Fred72z/ALICE/Cartouche/Etiquettes/4K_FlagonBird_Etiquette.png

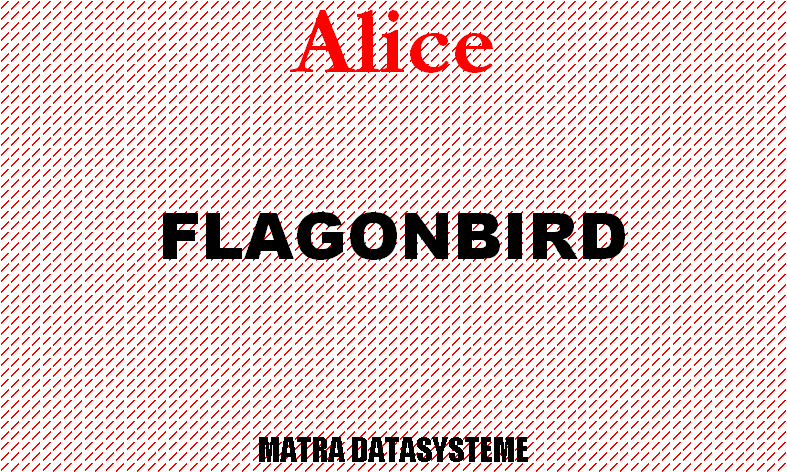
Cartouche/Etiquettes/4K_FlagonBird_Etiquette.png
