Fred72z/ALICE/Cartouche/Etiquettes/4K_LostWorld_Etiquette.png

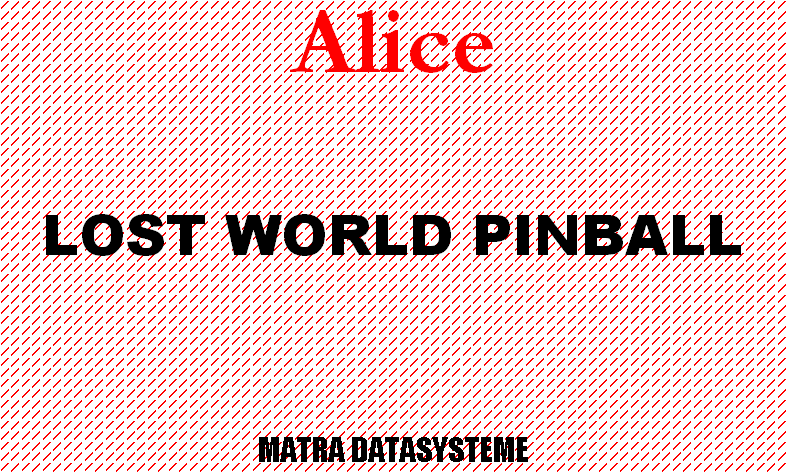
Cartouche/Etiquettes/4K_LostWorld_Etiquette.png
