Fred72z/ALICE/Cartouche/Etiquettes/Chenille_Etiquette.png

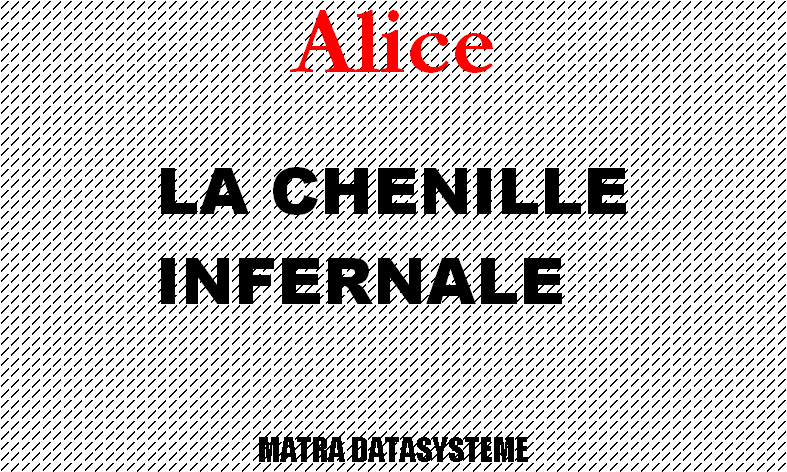
Cartouche/Etiquettes/Chenille_Etiquette.png
