Fred72z/ALICE/Cartouche/Etiquettes/Crocky_Etiquette.png

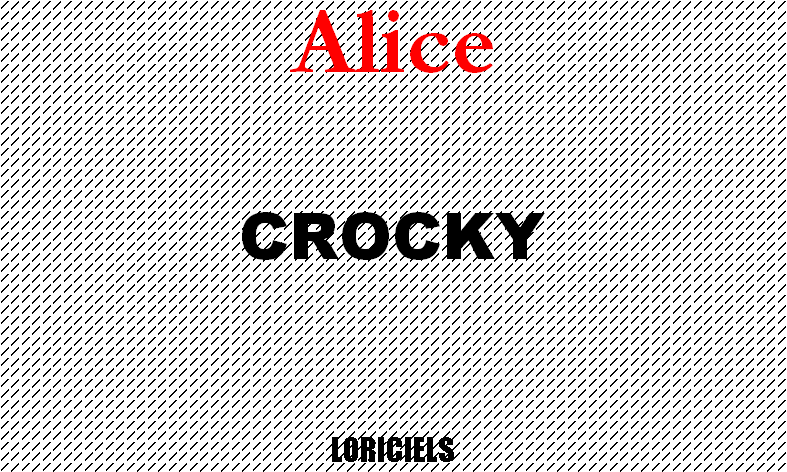
Cartouche/Etiquettes/Crocky_Etiquette.png
