Fred72z/ALICE/Cartouche/Etiquettes/Fringale_Etiquette.png

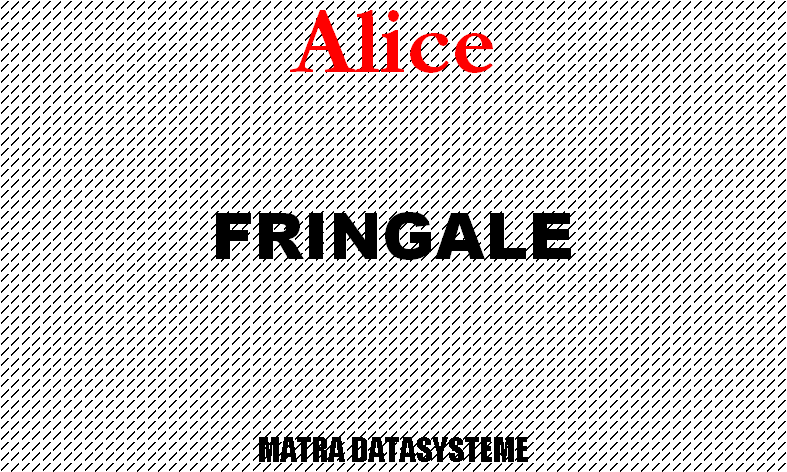
Cartouche/Etiquettes/Fringale_Etiquette.png
