Fred72z/ALICE/Cartouche/Etiquettes/PillageCosmique_Etiquette.png

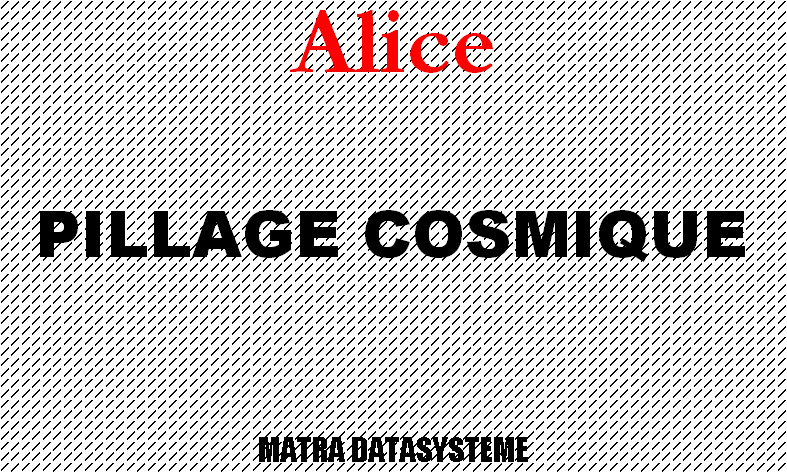
Cartouche/Etiquettes/PillageCosmique_Etiquette.png
