Fred72z/ALICE/Cartouche/Etiquettes/Tank_Etiquette.png

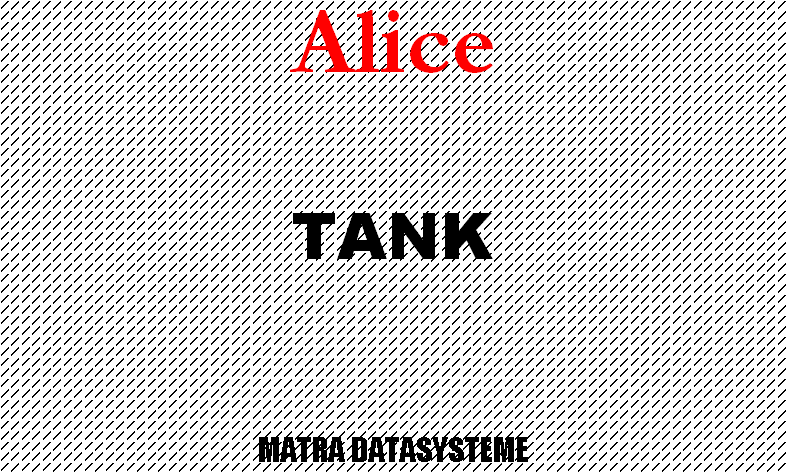
Cartouche/Etiquettes/Tank_Etiquette.png
