Fred72z/ALICE/Cartouche/Jaquettes/4K_FlagonBird_Jaquette.png

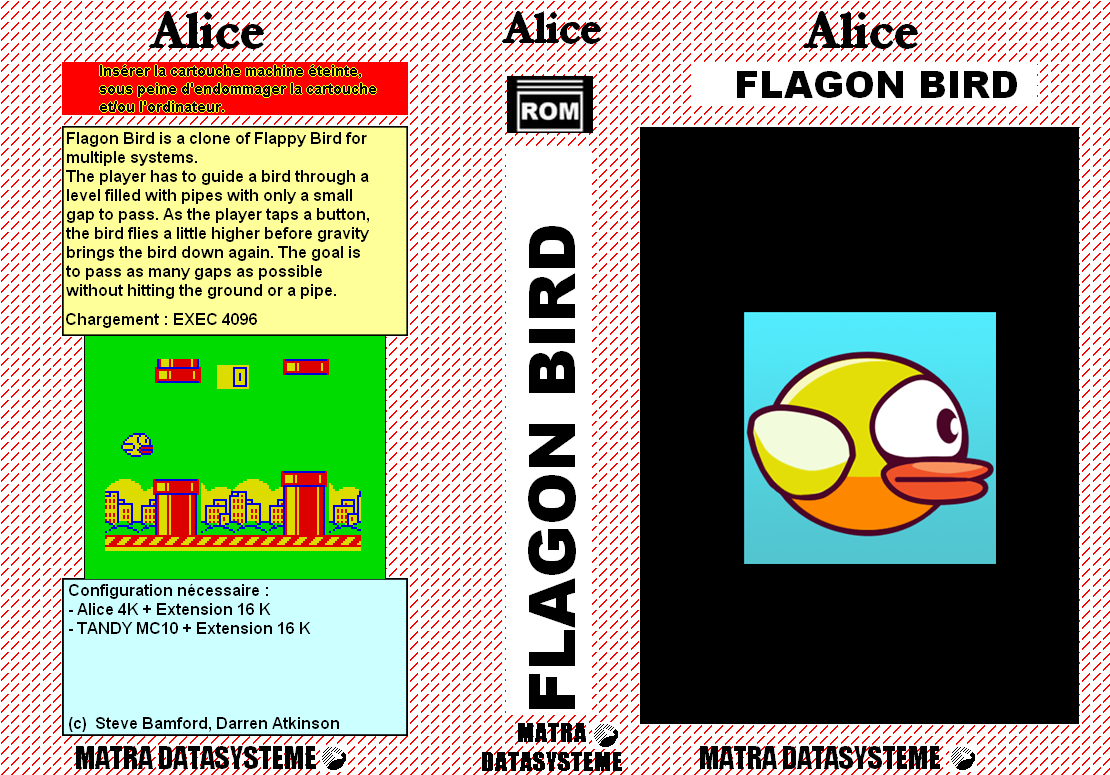
Cartouche/Jaquettes/4K_FlagonBird_Jaquette.png
