Fred72z/ALICE/Cartouche/Jaquettes/4K_Pacman_Jaquette.png

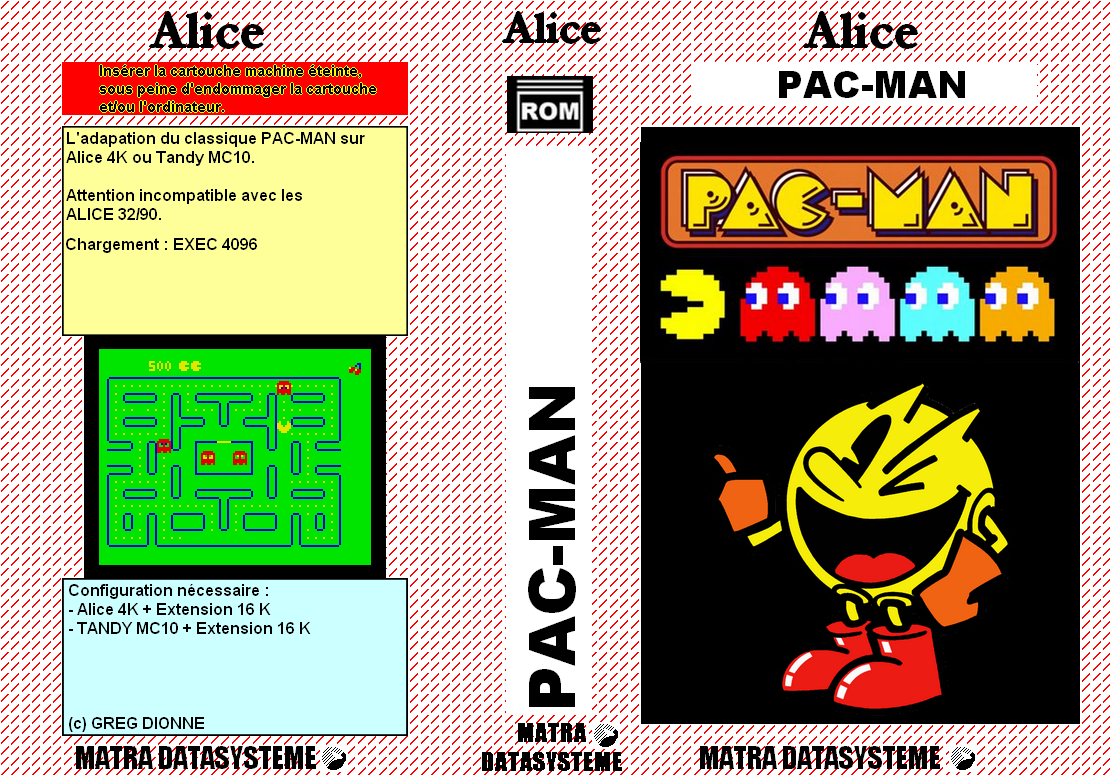
Cartouche/Jaquettes/4K_Pacman_Jaquette.png
