Fred72z/ALICE/Cartouche/Jaquettes/Chenille_Jaquette.png

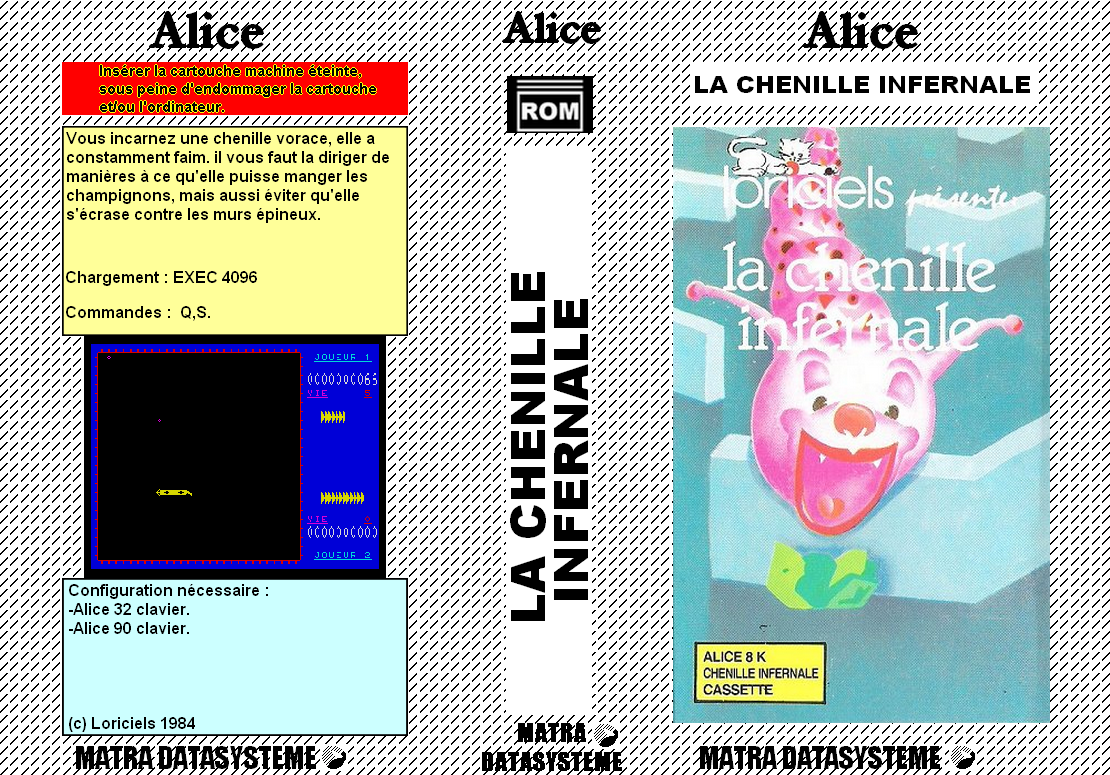
Cartouche/Jaquettes/Chenille_Jaquette.png
