Fred72z/ALICE/Cartouche/Jaquettes/Crocky_Jaquette.png

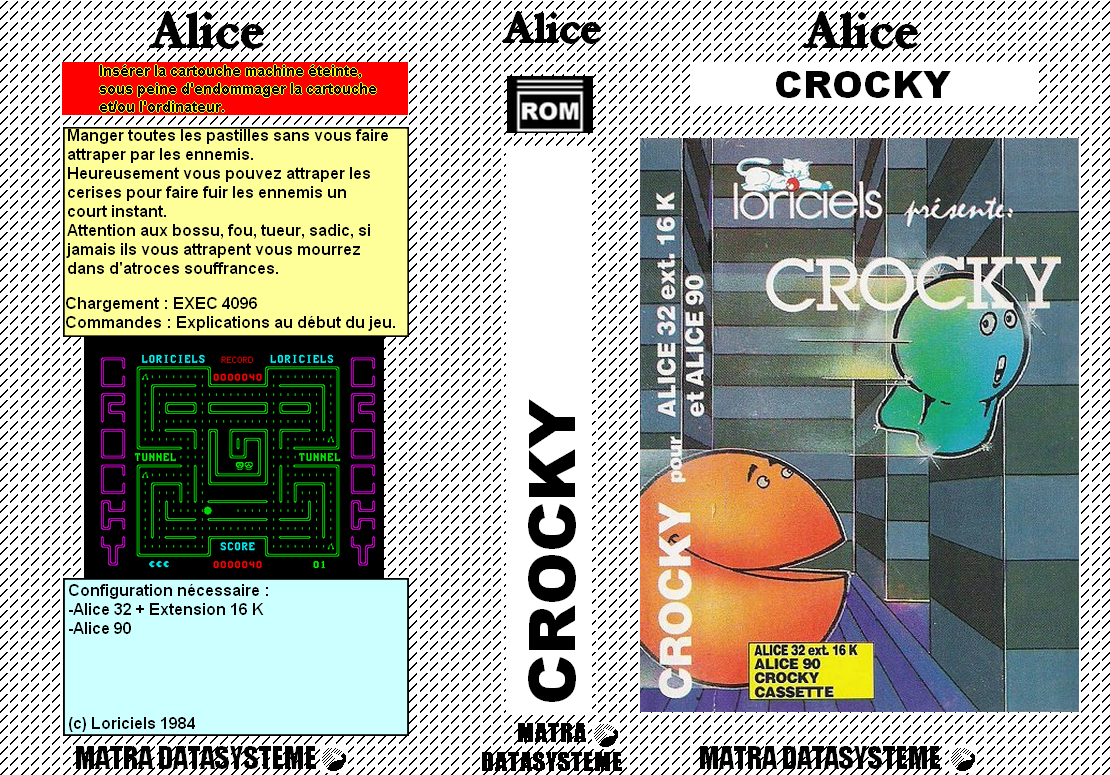
Cartouche/Jaquettes/Crocky_Jaquette.png
