Fred72z/ALICE/Cartouche/Jaquettes/DessineMoi_Jaquette.png

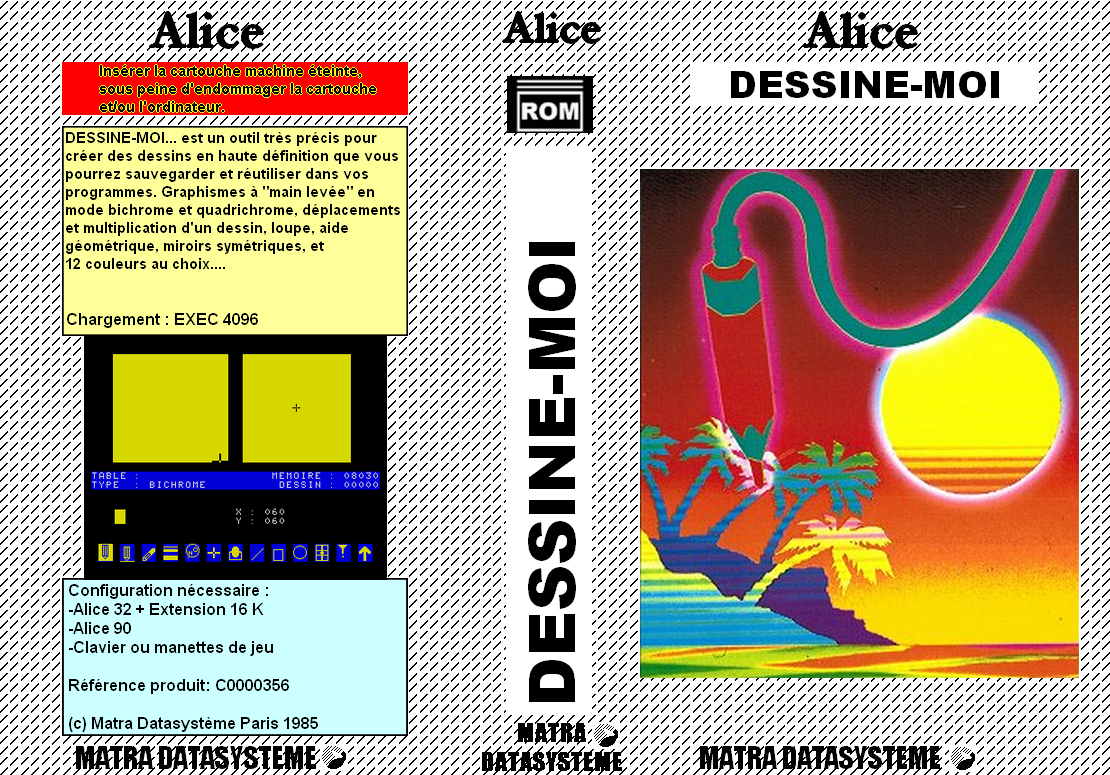
Cartouche/Jaquettes/DessineMoi_Jaquette.png
