Fred72z/ALICE/Cartouche/Jaquettes/Fringale90_Jaquette.png

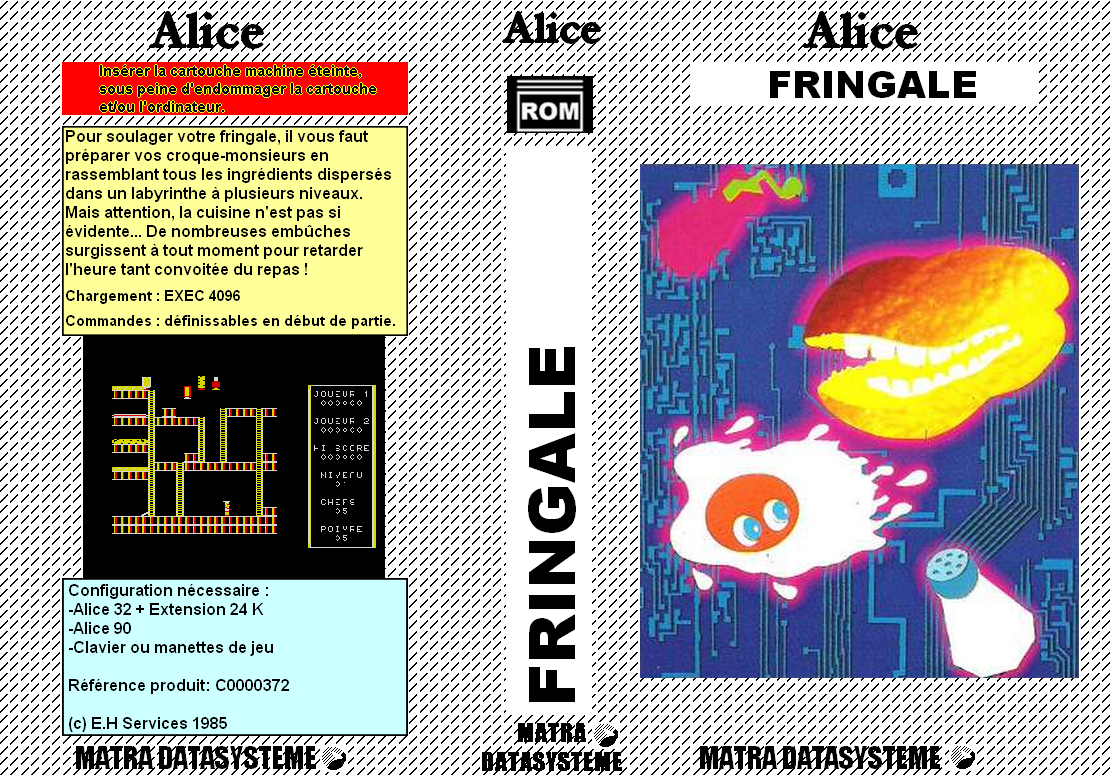
Cartouche/Jaquettes/Fringale90_Jaquette.png
