Fred72z/ALICE/Cartouche/Jaquettes/PillageCosmique_Jaquette.png

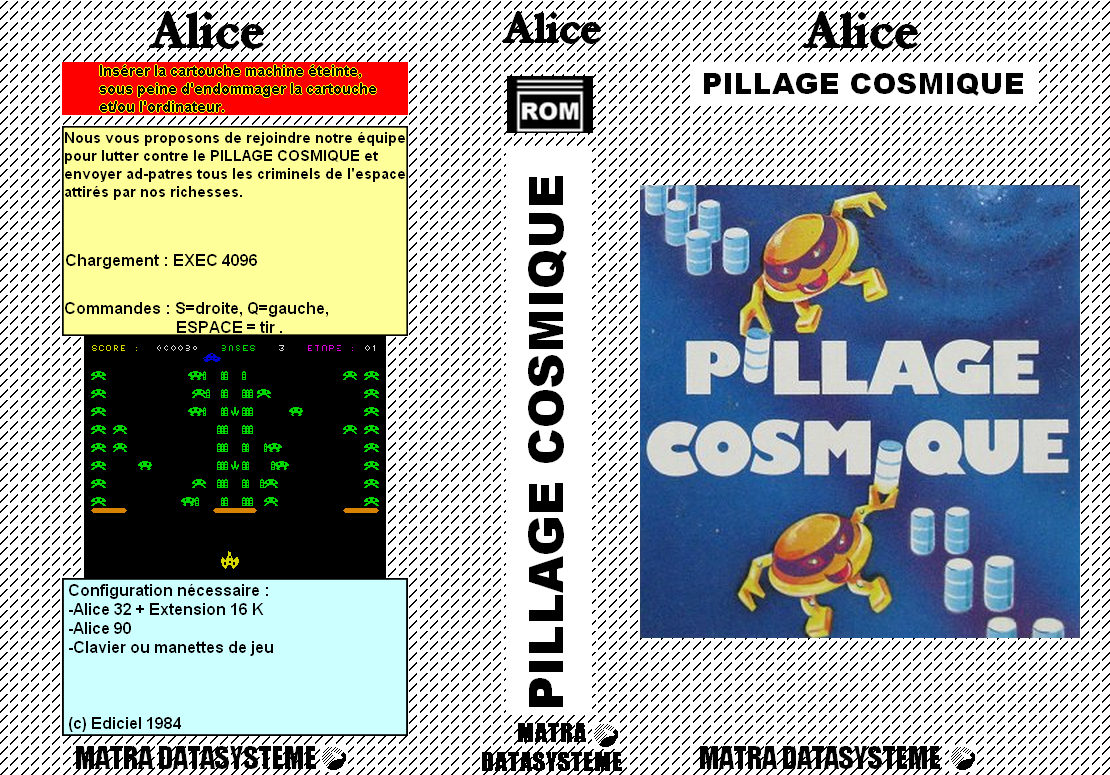
Cartouche/Jaquettes/PillageCosmique_Jaquette.png
