Fred72z/ALICE/Cartouche/Jaquettes/Tank_Jaquette.png

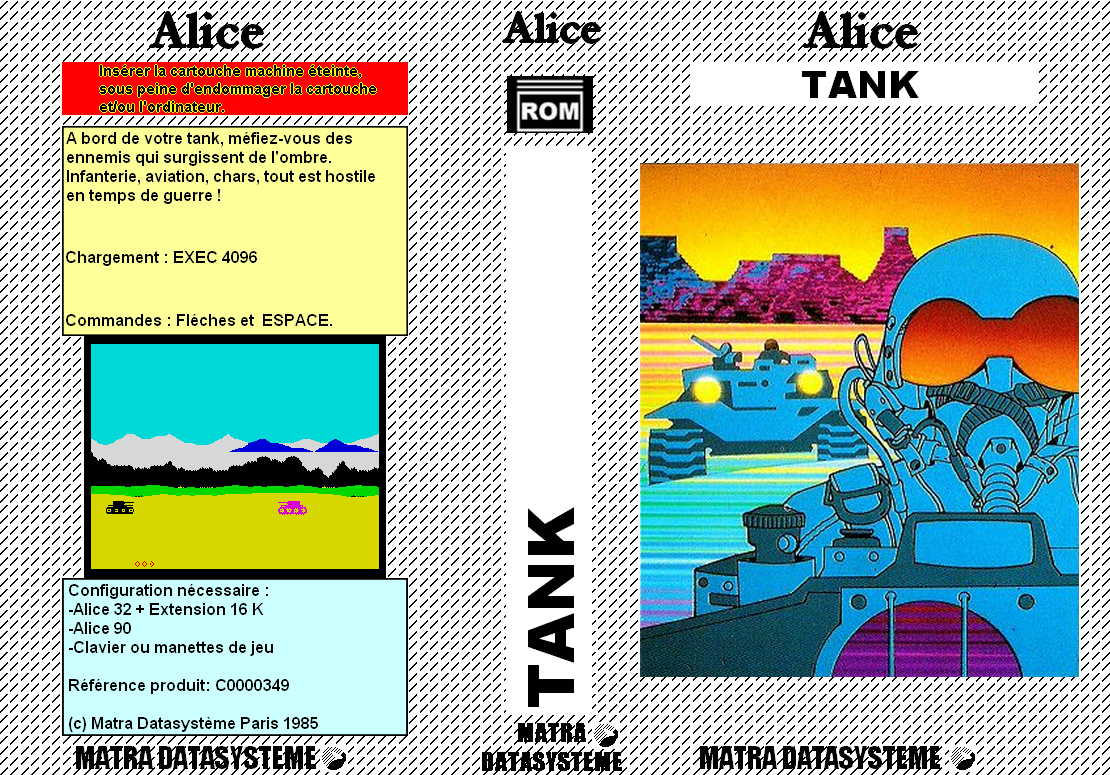
Cartouche/Jaquettes/Tank_Jaquette.png
